riturajtiwari/baybasi-panel/hw/enclosure/enc-kit.png

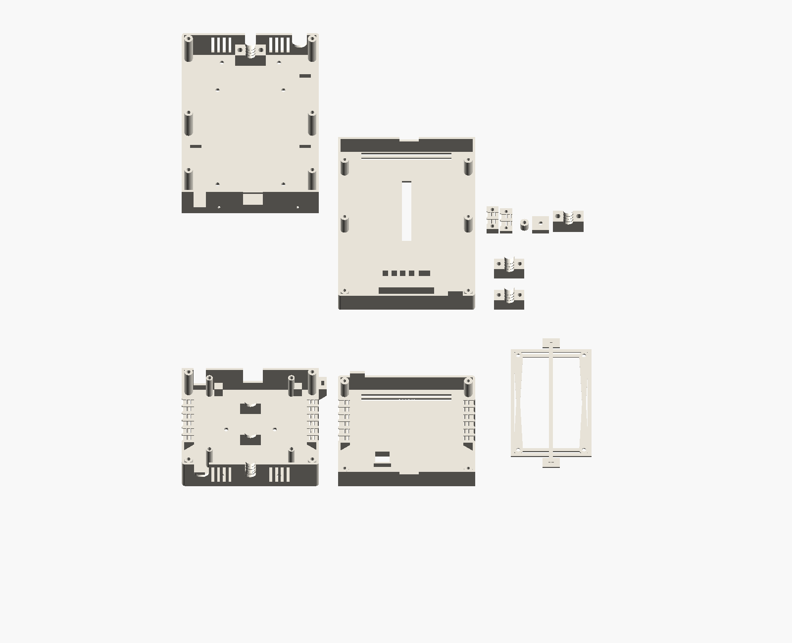
hw/enclosure/enc-kit.png
