riturajtiwari/baybasi-panel/hw/enclosure/enc-lid.png

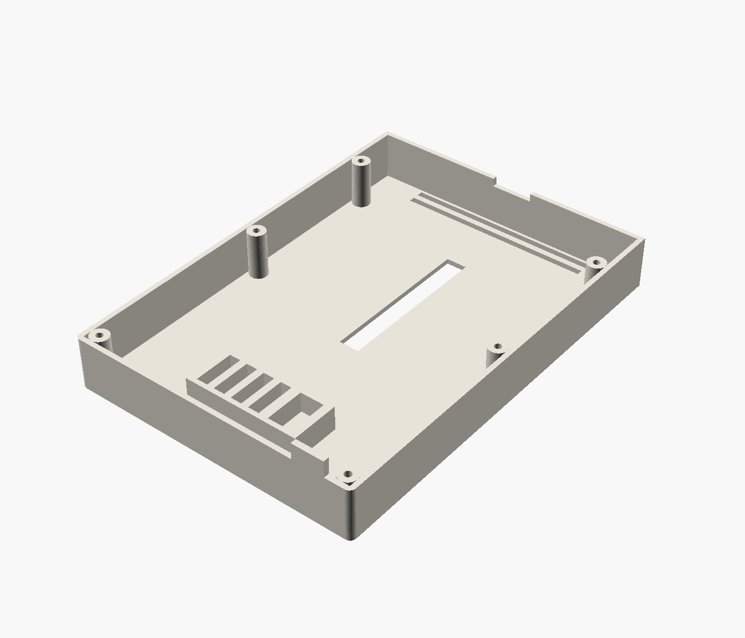
hw/enclosure/enc-lid.png
